Savio-Cardoz/theLink/components/epaper_driver_bsp/epaper_driver_bsp.h

#ifndef EPAPER_DRIVER_BSP_H
#define EPAPER_DRIVER_BSP_H

#include "driver/spi_master.h"
#include "driver/gpio.h"

/* Display color */
typedef enum {
    DRIVER_COLOR_WHITE  = 0xff,
    DRIVER_COLOR_BLACK  = 0x00,
    FONT_BACKGROUND = DRIVER_COLOR_WHITE,
}COLOR_IMAGE;

typedef struct {
    uint8_t cs;
    uint8_t dc;
    uint8_t rst;
    uint8_t busy;
    uint8_t mosi;
    uint8_t scl;
    int spi_host;
    int buffer_len;
}custom_lcd_spi_t;

class epaper_driver_display {
private:
    const custom_lcd_spi_t lcd_spi_data;
    const int Width;
    const int Height;
    spi_device_handle_t spi;
    uint8_t *buffer = NULL;

    void spi_gpio_init();
    void spi_port_init();
    void read_busy();

    esp_err_t spi_transmit_with_retry(spi_transaction_t *t, const char *what);

    void set_cs_1(){gpio_set_level((gpio_num_t)lcd_spi_data.cs,1);}
    void set_cs_0(){gpio_set_level((gpio_num_t)lcd_spi_data.cs,0);}
    void set_dc_1(){gpio_set_level((gpio_num_t)lcd_spi_data.dc,1);}
    void set_dc_0(){gpio_set_level((gpio_num_t)lcd_spi_data.dc,0);}
    void set_rst_1(){gpio_set_level((gpio_num_t)lcd_spi_data.rst,1);}
    void set_rst_0(){gpio_set_level((gpio_num_t)lcd_spi_data.rst,0);}

    void SPI_SendByte(uint8_t data);
    void EPD_SendData(uint8_t data);
    void EPD_SendCommand(uint8_t command);
    void writeBytes(uint8_t *buffer,int len);
    void writeBytes(const uint8_t *buffer, int len);
    void EPD_SetWindows(uint16_t Xstart, uint16_t Ystart, uint16_t Xend, uint16_t Yend);
    void EPD_SetCursor(uint16_t Xstart, uint16_t Ystart);
    void EPD_SetLut(const uint8_t *lut);
    void EPD_TurnOnDisplay();
    void EPD_TurnOnDisplayPart();

public:
    epaper_driver_display(int width, int height, custom_lcd_spi_t _lcd_spi_data);
    epaper_driver_display(int width, int height, custom_lcd_spi_t _lcd_spi_data, uint8_t *external_buffer);
    ~epaper_driver_display();

    void EPD_Init();    /* 墨水屏初始化 */
    void EPD_Clear();   /* 清空屏幕 */
    void EPD_Display(); /* 刷buffer到墨水屏 */
    
    /*局部刷新*/
    void EPD_DisplayPartBaseImage();
    void EPD_Init_Partial();
    void EPD_DisplayPart();
    void EPD_DrawColorPixel(uint16_t x, uint16_t y,uint8_t color);

    void EPD_LogHeap(const char *context);
};
#endif
