Savio-Cardoz/theLink/components/i2c_bsp/i2c_bsp.c

#include <string.h>

#include "driver/i2c_master.h"
#include "esp_log.h"
#include "freertos/FreeRTOS.h"
#include "freertos/task.h"

#include "i2c_bsp.h"

static const char *TAG = "I2C_BSP";

// Tag of the ESP-IDF I2C driver, silenced while sweeping so an absent device
// does not print an error per address.
static const char *DRIVER_TAG = "i2c.master";

// Mirrors the bus setup in the audio board support (components/codec_board/
// codec_init.c) so that a bus installed here behaves identically for the codec
// and RTC that share it.
#define I2C_BSP_GLITCH_IGNORE_CNT 7

// A probe of a present device finishes in a few hundred microseconds, so this
// only ever gets spent when a device holds the bus down.
#define I2C_BSP_SCAN_TIMEOUT_MS 20

// How many addresses must time out back to back before the sweep concludes the bus
// is stuck rather than busy. The driver reports "bus mutex unavailable" and "SDA
// held low" with the same error, and only the second is a wiring fault. A busy bus
// clears within one or two addresses, so a short run separates the two cases without
// needing to hold the bus quiet for longer than the sweep itself.
#define I2C_BSP_SCAN_STUCK_RUN 3

static i2c_master_bus_handle_t s_bus[I2C_BSP_MAX_PORTS];
static bool s_installed[I2C_BSP_MAX_PORTS];

esp_err_t i2c_bsp_init(uint8_t port, gpio_num_t sda, gpio_num_t scl)
{
    if (port >= I2C_BSP_MAX_PORTS)
    {
        ESP_LOGE(TAG, "I2C port %u out of range (max %d)", port, I2C_BSP_MAX_PORTS);
        return ESP_ERR_INVALID_ARG;
    }

    if (s_bus[port] != NULL)
    {
        return ESP_OK;
    }

    i2c_master_bus_config_t bus_config = {
        .clk_source = I2C_CLK_SRC_DEFAULT,
        .i2c_port = (i2c_port_num_t)port,
        .sda_io_num = sda,
        .scl_io_num = scl,
        .glitch_ignore_cnt = I2C_BSP_GLITCH_IGNORE_CNT,
        .flags.enable_internal_pullup = true,
    };

    i2c_master_bus_handle_t bus = NULL;
    esp_err_t err = i2c_new_master_bus(&bus_config, &bus);
    if (err == ESP_ERR_INVALID_STATE)
    {
        // Somebody got here first, most likely the audio board support, which
        // installs the bus itself from the audio task. Adopt their bus rather
        // than fighting over it.
        if (i2c_master_get_bus_handle((i2c_port_num_t)port, &bus) == ESP_OK && bus != NULL)
        {
            s_bus[port] = bus;
            s_installed[port] = false;
            ESP_LOGI(TAG, "Adopting existing I2C master bus on port %u", port);
            return ESP_OK;
        }
    }
    if (err != ESP_OK)
    {
        ESP_LOGE(TAG, "Failed to create I2C master bus on port %u: %s", port, esp_err_to_name(err));
        return err;
    }

    s_bus[port] = bus;
    s_installed[port] = true;
    ESP_LOGI(TAG, "I2C master bus %d up on SDA %d / SCL %d", port, sda, scl);
    return ESP_OK;
}

i2c_master_bus_handle_t i2c_bsp_bus(uint8_t port)
{
    if (port >= I2C_BSP_MAX_PORTS)
    {
        return NULL;
    }
    return s_bus[port];
}

void i2c_bsp_deinit(void)
{
    for (uint8_t port = 0; port < I2C_BSP_MAX_PORTS; port++)
    {
        if (!s_installed[port])
        {
            continue;
        }
        ESP_LOGI(TAG, "Deleting I2C master bus on port %u", port);
        i2c_del_master_bus(s_bus[port]);
        s_bus[port] = NULL;
        s_installed[port] = false;
    }
}

esp_err_t i2c_bsp_scan(uint8_t port, uint8_t first_addr, uint8_t last_addr,
                       uint8_t *found, size_t found_cap, size_t *found_count)
{
    if (port >= I2C_BSP_MAX_PORTS)
    {
        ESP_LOGE(TAG, "I2C port %u out of range (max %d)", port, I2C_BSP_MAX_PORTS);
        return ESP_ERR_INVALID_ARG;
    }
    if (first_addr > last_addr || last_addr > 0x7F)
    {
        ESP_LOGE(TAG, "I2C scan range 0x%02X..0x%02X is not a valid 7-bit range", first_addr, last_addr);
        return ESP_ERR_INVALID_ARG;
    }
    if (found == NULL || found_count == NULL)
    {
        return ESP_ERR_INVALID_ARG;
    }
    if (s_bus[port] == NULL)
    {
        return ESP_ERR_INVALID_STATE;
    }

    *found_count = 0;

    // The driver logs every address-only write that comes back NACKed, which on
    // a mostly empty bus is most of them. Mute it for the sweep only.
    const esp_log_level_t driver_level = esp_log_level_get(DRIVER_TAG);
    esp_log_level_set(DRIVER_TAG, ESP_LOG_NONE);

    esp_err_t ret = ESP_OK;
    size_t probed = 0;
    size_t nacked = 0;
    size_t timeouts = 0;
    unsigned consecutive_timeouts = 0;

    for (unsigned addr = first_addr; addr <= last_addr; addr++)
    {
        // The driver takes the bus mutex for the probe, so a codec write or a sensor
        // read still in flight makes the probe wait. Waits for that here rather
        // than reporting the resulting timeout as a missing device.
        (void)i2c_master_bus_wait_all_done(s_bus[port], pdMS_TO_TICKS(I2C_BSP_SCAN_TIMEOUT_MS));

        const esp_err_t err = i2c_master_probe(s_bus[port], (uint16_t)addr, I2C_BSP_SCAN_TIMEOUT_MS);
        probed++;
        if (err == ESP_OK)
        {
            consecutive_timeouts = 0;
            ESP_LOGD(TAG, "0x%02X acknowledged", addr);
            if (*found_count < found_cap)
            {
                found[(*found_count)++] = (uint8_t)addr;
            }
            else
            {
                // Not fatal, but the list is now incomplete, so a reader must not
                // treat it as proof the bus holds nothing else.
                ESP_LOGW(TAG, "more than %zu devices answered, the list is truncated", found_cap);
                ret = ESP_ERR_INVALID_SIZE;
            }
            continue;
        }

        if (err == ESP_ERR_TIMEOUT)
        {
            // The driver reports a bus mutex timeout as ESP_ERR_TIMEOUT too, so this
            // is not on its own evidence of a broken bus. Only a run of them is: a
            // genuine stuck-bus fault keeps timing out at every address, whereas a
            // busy bus recovers.
            timeouts++;
            consecutive_timeouts++;
            ESP_LOGD(TAG, "0x%02X timed out (bus busy, or held low)", addr);
            if (consecutive_timeouts >= I2C_BSP_SCAN_STUCK_RUN)
            {
                ret = ESP_ERR_TIMEOUT;
                break;
            }
            continue;
        }

        consecutive_timeouts = 0;
        nacked++;
        ESP_LOGD(TAG, "0x%02X did not acknowledge", addr);
    }

    // Every result, not just the hits. A sweep that reports five addresses is
    // indistinguishable from one that silently stopped early unless the misses are
    // visible too, which is what makes an absent device tellable apart from a probe
    // that never ran.
    ESP_LOGI(TAG, "swept 0x%02X..0x%02X: %zu answered, %zu did not acknowledge, %zu timed out",
             first_addr, last_addr, probed - nacked - timeouts, nacked, timeouts);

    esp_log_level_set(DRIVER_TAG, driver_level);
    return ret;
}
