Savio-Cardoz/theLink/main/provisioning.cpp

#include <stdio.h>
#include <string.h>
#include <atomic>

#include "freertos/FreeRTOS.h"
#include "freertos/task.h"
#include "freertos/event_groups.h"

#include "esp_log.h"
#include "esp_err.h"
#include "esp_wifi.h"
#include "esp_event.h"
#include "esp_system.h"
#include "esp_heap_caps.h"

#include <network_provisioning/manager.h>
#include <network_provisioning/scheme_ble.h>
#include "qrcode.h"

#include "lvgl.h"

#include "app_common.hpp"
#include "download_mgr.hpp"
#include "mqtt_io.hpp"
#include "ui_port.hpp"

#include "provisioning.hpp"

static const char *TAG = "app";

static std::atomic<led_prov_state_t> s_led_prov_state{led_prov_state_t::LED_PROV_STATE_NONE};

static void (*s_post_provision_hook)(void) = nullptr;

uint32_t prov_pulse_period_ms(led_prov_state_t state)
{
	switch (state) {
	case led_prov_state_t::LED_PROV_STATE_PROVISIONING:   return 500;
	case led_prov_state_t::LED_PROV_STATE_BLE_CONNECTED:  return 1500;
	case led_prov_state_t::LED_PROV_STATE_WIFI_CONNECTED: return 3000;
	default:                                              return 0;
	}
}

void prov_set_led_state(led_prov_state_t state)
{
	s_led_prov_state.store(state);
}

led_prov_state_t prov_get_led_state(void)
{
	return s_led_prov_state.load();
}

// ── Wi-Fi provisioning definitions ──────────────────────────────────
#if CONFIG_EXAMPLE_PROV_SECURITY_VERSION_2
#if CONFIG_EXAMPLE_PROV_SEC2_DEV_MODE
#define PROV_SEC2_USERNAME "wifiprov"
#define PROV_SEC2_PWD "abcd1234"

/* This salt,verifier has been generated for username = "wifiprov" and password = "abcd1234"
 * IMPORTANT NOTE: For production cases, this must be unique to every device
 * and should come from device manufacturing partition.*/
static const char sec2_salt[] = {
	0x03, 0x6e, 0xe0, 0xc7, 0xbc, 0xb9, 0xed, 0xa8, 0x4c, 0x9e, 0xac, 0x97, 0xd9, 0x3d, 0xec, 0xf4};

static const char sec2_verifier[] = {
	0x7c, 0x7c, 0x85, 0x47, 0x65, 0x08, 0x94, 0x6d, 0xd6, 0x36, 0xaf, 0x37, 0xd7, 0xe8, 0x91, 0x43,
	0x78, 0xcf, 0xfd, 0x61, 0x6c, 0x59, 0xd2, 0xf8, 0x39, 0x08, 0x12, 0x72, 0x38, 0xde, 0x9e, 0x24,
	0xa4, 0x70, 0x26, 0x1c, 0xdf, 0xa9, 0x03, 0xc2, 0xb2, 0x70, 0xe7, 0xb1, 0x32, 0x24, 0xda, 0x11,
	0x1d, 0x97, 0x18, 0xdc, 0x60, 0x72, 0x08, 0xcc, 0x9a, 0xc9, 0x0c, 0x48, 0x27, 0xe2, 0xae, 0x89,
	0xaa, 0x16, 0x25, 0xb8, 0x04, 0xd2, 0x1a, 0x9b, 0x3a, 0x8f, 0x37, 0xf6, 0xe4, 0x3a, 0x71, 0x2e,
	0xe1, 0x27, 0x86, 0x6e, 0xad, 0xce, 0x28, 0xff, 0x54, 0x46, 0x60, 0x1f, 0xb9, 0x96, 0x87, 0xdc,
	0x57, 0x40, 0xa7, 0xd4, 0x6c, 0xc9, 0x77, 0x54, 0xdc, 0x16, 0x82, 0xf0, 0xed, 0x35, 0x6a, 0xc4,
	0x70, 0xad, 0x3d, 0x90, 0xb5, 0x81, 0x94, 0x70, 0xd7, 0xbc, 0x65, 0xb2, 0xd5, 0x18, 0xe0, 0x2e,
	0xc3, 0xa5, 0xf9, 0x68, 0xdd, 0x64, 0x7b, 0xb8, 0xb7, 0x3c, 0x9c, 0xfc, 0x00, 0xd8, 0x71, 0x7e,
	0xb7, 0x9a, 0x7c, 0xb1, 0xb7, 0xc2, 0xc3, 0x18, 0x34, 0x29, 0x32, 0x43, 0x3e, 0x00, 0x99, 0xe9,
	0x82, 0x94, 0xe3, 0xd8, 0x2a, 0xb0, 0x96, 0x29, 0xb7, 0xdf, 0x0e, 0x5f, 0x08, 0x33, 0x40, 0x76,
	0x52, 0x91, 0x32, 0x00, 0x9f, 0x97, 0x2c, 0x89, 0x6c, 0x39, 0x1e, 0xc8, 0x28, 0x05, 0x44, 0x17,
	0x3f, 0x68, 0x02, 0x8a, 0x9f, 0x44, 0x61, 0xd1, 0xf5, 0xa1, 0x7e, 0x5a, 0x70, 0xd2, 0xc7, 0x23,
	0x81, 0xcb, 0x38, 0x68, 0xe4, 0x2c, 0x20, 0xbc, 0x40, 0x57, 0x76, 0x17, 0xbd, 0x08, 0xb8, 0x96,
	0xbc, 0x26, 0xeb, 0x32, 0x46, 0x69, 0x35, 0x05, 0x8c, 0x15, 0x70, 0xd9, 0x1b, 0xe9, 0xbe, 0xcc,
	0xa9, 0x38, 0xa6, 0x67, 0xf0, 0xad, 0x50, 0x13, 0x19, 0x72, 0x64, 0xbf, 0x52, 0xc2, 0x34, 0xe2,
	0x1b, 0x11, 0x79, 0x74, 0x72, 0xbd, 0x34, 0x5b, 0xb1, 0xe2, 0xfd, 0x66, 0x73, 0xfe, 0x71, 0x64,
	0x74, 0xd0, 0x4e, 0xbc, 0x51, 0x24, 0x19, 0x40, 0x87, 0x0e, 0x92, 0x40, 0xe6, 0x21, 0xe7, 0x2d,
	0x4e, 0x37, 0x76, 0x2f, 0x2e, 0xe2, 0x68, 0xc7, 0x89, 0xe8, 0x32, 0x13, 0x42, 0x06, 0x84, 0x84,
	0x53, 0x4a, 0xb3, 0x0c, 0x1b, 0x4c, 0x8d, 0x1c, 0x51, 0x97, 0x19, 0xab, 0xae, 0x77, 0xff, 0xdb,
	0xec, 0xf0, 0x10, 0x95, 0x34, 0x33, 0x6b, 0xcb, 0x3e, 0x84, 0x0f, 0xb9, 0xd8, 0x5f, 0xb8, 0xa0,
	0xb8, 0x55, 0x53, 0x3e, 0x70, 0xf7, 0x18, 0xf5, 0xce, 0x7b, 0x4e, 0xbf, 0x27, 0xce, 0xce, 0xa8,
	0xb3, 0xbe, 0x40, 0xc5, 0xc5, 0x32, 0x29, 0x3e, 0x71, 0x64, 0x9e, 0xde, 0x8c, 0xf6, 0x75, 0xa1,
	0xe6, 0xf6, 0x53, 0xc8, 0x31, 0xa8, 0x78, 0xde, 0x50, 0x40, 0xf7, 0x62, 0xde, 0x36, 0xb2, 0xba};
#endif

static esp_err_t example_get_sec2_salt(const char **salt, uint16_t *salt_len)
{
#if CONFIG_EXAMPLE_PROV_SEC2_DEV_MODE
	ESP_LOGI(TAG, "Development mode: using hard coded salt");
	*salt = sec2_salt;
	*salt_len = sizeof(sec2_salt);
	return ESP_OK;
#elif CONFIG_EXAMPLE_PROV_SEC2_PROD_MODE
	ESP_LOGE(TAG, "Not implemented!");
	return ESP_FAIL;
#endif
}

static esp_err_t example_get_sec2_verifier(const char **verifier, uint16_t *verifier_len)
{
#if CONFIG_EXAMPLE_PROV_SEC2_DEV_MODE
	ESP_LOGI(TAG, "Development mode: using hard coded verifier");
	*verifier = sec2_verifier;
	*verifier_len = sizeof(sec2_verifier);
	return ESP_OK;
#elif CONFIG_EXAMPLE_PROV_SEC2_PROD_MODE
	/* This code needs to be updated with appropriate implementation to provide verifier */
	ESP_LOGE(TAG, "Not implemented!");
	return ESP_FAIL;
#endif
}
#endif

// Persistent structures for the live binary QR matrix layout engine
static lv_image_dsc_t qr_dynamic_bmp;
static uint8_t *qr_pixel_buffer = NULL;
static lv_obj_t *qr_image_obj = NULL;

#define PROV_QR_VERSION "v1"
#define PROV_TRANSPORT_SOFTAP "softap"
#define PROV_TRANSPORT_BLE "ble"
#define QRCODE_BASE_URL "https://espressif.github.io/esp-jumpstart/qrcode.html"

/* How long to keep retrying the MQTT client start. 1 s apart, so this covers
 * both ways provisioning ends: the client hanging up (a few seconds) and the
 * network_provisioning auto-stop timer (CONFIG_NETWORK_PROV_AUTOSTOP_TIMEOUT,
 * 30 s by default). */
#define MQTT_START_MAX_ATTEMPTS 60

/* Signal Wi-Fi events on this event-group */
const int WIFI_CONNECTED_EVENT = BIT0;
static EventGroupHandle_t wifi_event_group;

static void wifi_init_sta(void)
{
	/* Start Wi-Fi in station mode */
	ESP_ERROR_CHECK(esp_wifi_set_mode(WIFI_MODE_STA));
	ESP_ERROR_CHECK(esp_wifi_start());
}

static void wifi_prov_task(void *arg);

static void get_device_service_name(char *service_name, size_t max)
{
	uint8_t eth_mac[6];
	const char *ssid_prefix = "PROV_";
	esp_wifi_get_mac(WIFI_IF_STA, eth_mac);
	snprintf(service_name, max, "%s%02X%02X%02X",
			 ssid_prefix, eth_mac[3], eth_mac[4], eth_mac[5]);
}

/* Handler for the optional provisioning endpoint registered by the application.
 * The data format can be chosen by applications. Here, we are using plain ascii text.
 * Applications can choose to use other formats like protobuf, JSON, XML, etc.
 * Note that memory for the response buffer must be allocated using heap as this buffer
 * gets freed by the protocomm layer once it has been sent by the transport layer.
 */
esp_err_t custom_prov_data_handler(uint32_t session_id, const uint8_t *inbuf, ssize_t inlen,
								   uint8_t **outbuf, ssize_t *outlen, void *priv_data)
{
	if (inbuf)
	{
		ESP_LOGI(TAG, "Received data: %.*s", inlen, (char *)inbuf);
	}
	char response[] = "SUCCESS";
	*outbuf = (uint8_t *)strdup(response);
	if (*outbuf == NULL)
	{
		ESP_LOGE(TAG, "System out of memory");
		return ESP_ERR_NO_MEM;
	}
	*outlen = strlen(response) + 1; /* +1 for NULL terminating byte */

	return ESP_OK;
}

static void qr_code_lvgl_display_cb(esp_qrcode_handle_t qrcode) {
    int qr_size = esp_qrcode_get_size(qrcode);
    const int display_dim = 200;

    ESP_LOGI("QR_UI", "callback entered: qr_size=%d, SPIRAM free=%u",
             qr_size, (unsigned)heap_caps_get_free_size(MALLOC_CAP_SPIRAM));

    int scale = display_dim / qr_size;
    if (scale < 1) scale = 1;

    int offset_x = (display_dim - (qr_size * scale)) / 2;
    int offset_y = (display_dim - (qr_size * scale)) / 2;

    const size_t RGB565_SIZE = display_dim * display_dim * 2;

    if (qr_pixel_buffer == NULL) {
        qr_pixel_buffer = (uint8_t *)heap_caps_malloc(RGB565_SIZE, MALLOC_CAP_SPIRAM);
    }

    if (qr_pixel_buffer == NULL) {
        ESP_LOGE("QR_UI", "External frame allocation breakdown for QR matrix layer!");
        return;
    }

    ESP_LOGI("QR_UI", "qr_pixel_buffer=%p, scale=%d, offset=(%d,%d)",
             (void *)qr_pixel_buffer, scale, offset_x, offset_y);

    uint16_t *rgb565_dest = (uint16_t *)qr_pixel_buffer;
    for (int i = 0; i < (display_dim * display_dim); i++) {
        rgb565_dest[i] = 0xFFFF; // Clear canvas background to complete white
    }

    for (int y = 0; y < qr_size; y++) {
        for (int x = 0; x < qr_size; x++) {
            if (esp_qrcode_get_module(qrcode, x, y)) {
                for (int py = 0; py < scale; py++) {
                    for (int px = 0; px < scale; px++) {
                        int target_x = offset_x + (x * scale) + px;
                        int target_y = offset_y + (y * scale) + py;
                        if (target_x >= 0 && target_x < display_dim && target_y >= 0 && target_y < display_dim) {
                            rgb565_dest[target_y * display_dim + target_x] = 0x0000; // Map black module bits
                        }
                    }
                }
            }
        }
    }

    qr_dynamic_bmp.header.magic = LV_IMAGE_HEADER_MAGIC;
    qr_dynamic_bmp.header.cf = LV_COLOR_FORMAT_RGB565;
    qr_dynamic_bmp.header.flags = 0;
    qr_dynamic_bmp.header.w = display_dim;
    qr_dynamic_bmp.header.h = display_dim;
    qr_dynamic_bmp.header.stride = display_dim * 2;
    qr_dynamic_bmp.header.reserved_2 = 0;
    qr_dynamic_bmp.data_size = RGB565_SIZE;
    qr_dynamic_bmp.data = qr_pixel_buffer;

    bool locked = ui_lock(-1);
    ESP_LOGI("QR_UI", "ui_lock returned %d", locked);

    if (locked) {
        if (qr_image_obj == NULL) {
            qr_image_obj = lv_image_create(lv_screen_active());
        }

        lv_image_set_src(qr_image_obj, NULL);
        lv_image_set_src(qr_image_obj, &qr_dynamic_bmp);
        lv_obj_center(qr_image_obj);
        lv_obj_move_foreground(qr_image_obj);
        lv_obj_clear_flag(qr_image_obj, LV_OBJ_FLAG_HIDDEN);
        lv_obj_invalidate(qr_image_obj);

        ui_unlock();
        ESP_LOGI("QR_UI", "Successfully pushed binary QR image payload onto layout engine matrix.");
    }
}

static void wifi_prov_print_qr(const char *name, const char *username, const char *pop, const char *transport)
{
	if (!name || !transport)
	{
		ESP_LOGW(TAG, "Cannot generate QR code payload. Data missing.");
		return;
	}
	char payload[150] = {0};
	if (pop)
	{
#if CONFIG_EXAMPLE_PROV_SECURITY_VERSION_1
		snprintf(payload, sizeof(payload), "{\"ver\":\"%s\",\"name\":\"%s\""
										   ",\"pop\":\"%s\",\"transport\":\"%s\"}",
				 PROV_QR_VERSION, name, pop, transport);
#elif CONFIG_EXAMPLE_PROV_SECURITY_VERSION_2
		snprintf(payload, sizeof(payload), "{\"ver\":\"%s\",\"name\":\"%s\""
										   ",\"username\":\"%s\",\"pop\":\"%s\",\"transport\":\"%s\"}",
				 PROV_QR_VERSION, name, username, pop, transport);
#endif
	}
	else
	{
		snprintf(payload, sizeof(payload), "{\"ver\":\"%s\",\"name\":\"%s\""
										   ",\"transport\":\"%s\",\"network\":\"wifi\"}",
				 PROV_QR_VERSION, name, transport);
	}

	ESP_LOGI(TAG, "Scan this QR code from the provisioning application for Provisioning.");
	esp_qrcode_config_t cfg = ESP_QRCODE_CONFIG_DEFAULT();
	cfg.display_func = qr_code_lvgl_display_cb;
	esp_qrcode_generate(&cfg, payload);
	ESP_LOGI(TAG, "If QR code is not visible, copy paste the below URL in a browser.\n%s?data=%s", QRCODE_BASE_URL, payload);
}

#ifdef CONFIG_EXAMPLE_PROV_ENABLE_APP_CALLBACK
void wifi_prov_app_callback(void *user_data, wifi_prov_cb_event_t event, void *event_data)
{
	/**
	 * This is blocking callback, any configurations that needs to be set when a particular
	 * provisioning event is triggered can be set here.
	 */
	switch (event)
	{
	case WIFI_PROV_SET_STA_CONFIG:
	{
		/**
		 * Wi-Fi configurations can be set here before the Wi-Fi is enabled in
		 * STA mode.
		 */
		wifi_config_t *wifi_config = (wifi_config_t *)event_data;
		(void)wifi_config;
		break;
	}
	default:
		break;
	}
}

const wifi_prov_event_handler_t wifi_prov_event_handler = {
	.event_cb = wifi_prov_app_callback,
	.user_data = NULL,
};
#endif /* EXAMPLE_PROV_ENABLE_APP_CALLBACK */

static void event_handler(void *arg, esp_event_base_t event_base,
						  int32_t event_id, void *event_data)
{
	if (event_base == NETWORK_PROV_EVENT)
	{
		switch (event_id)
		{
		case NETWORK_PROV_START:
			ESP_LOGI(TAG, "Provisioning started");
			prov_set_led_state(led_prov_state_t::LED_PROV_STATE_PROVISIONING);
			break;
		case NETWORK_PROV_WIFI_CRED_RECV:
		{
			wifi_sta_config_t *wifi_sta_cfg = (wifi_sta_config_t *)event_data;
			ESP_LOGI(TAG, "Received Wi-Fi credentials"
						  "\n\tSSID     : %s\n\tPassword : %s",
					 (const char *)wifi_sta_cfg->ssid,
					 (const char *)wifi_sta_cfg->password);
			break;
		}
		case NETWORK_PROV_WIFI_CRED_FAIL:
		{
			network_prov_wifi_sta_fail_reason_t *reason = (network_prov_wifi_sta_fail_reason_t *)event_data;
			ESP_LOGE(TAG, "Provisioning failed!\n\tReason : %s"
						  "\n\tPlease reset to factory and retry provisioning",
					 (*reason == NETWORK_PROV_WIFI_STA_AUTH_ERROR) ? "Wi-Fi station authentication failed" : "Wi-Fi access-point not found");
#ifdef CONFIG_EXAMPLE_RESET_PROV_MGR_ON_FAILURE
			/* Reset the state machine on provisioning failure.
			 * This is enabled by the CONFIG_EXAMPLE_RESET_PROV_MGR_ON_FAILURE configuration.
			 * It allows the provisioning manager to retry the provisioning process
			 * based on the number of attempts specified in wifi_conn_attempts. After attempting
			 * the maximum number of retries, the provisioning manager will reset the state machine
			 * and the provisioning process will be terminated.
			 */
			network_prov_mgr_reset_wifi_sm_state_on_failure();
#endif
			break;
		}
		case NETWORK_PROV_WIFI_CRED_SUCCESS:
			ESP_LOGI(TAG, "Provisioning successful");
			break;
		case NETWORK_PROV_END:
		{
			/* De-initialize manager once provisioning is finished */
			esp_err_t err = network_prov_mgr_deinit();
			if (err != ESP_OK)
			{
				ESP_LOGE(TAG, "Failed to de-initialize provisioning manager: %s", esp_err_to_name(err));
			}

			// Clean up the binary image widget & its PSRAM allocation buffer
            if (ui_lock(-1))
            {
                if (qr_image_obj != NULL)
                {
                    lv_obj_delete(qr_image_obj);
                    qr_image_obj = NULL;
                }
                if (qr_pixel_buffer != NULL)
                {
                    heap_caps_free(qr_pixel_buffer);
                    qr_pixel_buffer = NULL;
                }
                lv_obj_invalidate(lv_screen_active());
                ui_unlock();
            }
			break;
		}
		default:
			break;
		}
	}
	else if (event_base == WIFI_EVENT)
	{
		switch (event_id)
		{
		case WIFI_EVENT_STA_START:
			esp_wifi_connect();
			break;
		case WIFI_EVENT_STA_DISCONNECTED:
			{
				ESP_LOGI(TAG, "Disconnected. Connecting to the AP again...");
				ui_notify_network_status(false);
				esp_wifi_connect();
			}
			break;
#ifdef CONFIG_EXAMPLE_PROV_TRANSPORT_SOFTAP
		case WIFI_EVENT_AP_STACONNECTED:
			ESP_LOGI(TAG, "SoftAP transport: Connected!");
			break;
		case WIFI_EVENT_AP_STADISCONNECTED:
			ESP_LOGI(TAG, "SoftAP transport: Disconnected!");
			break;
#endif
		default:
			break;
		}
	}
	else if (event_base == IP_EVENT && event_id == IP_EVENT_STA_GOT_IP)
	{
		ip_event_got_ip_t *event = (ip_event_got_ip_t *)event_data;
		ESP_LOGI(TAG, "Connected with IP Address:" IPSTR, IP2STR(&event->ip_info.ip));

		ui_notify_network_status(true);

		/* Signal main application to continue execution */
		xEventGroupSetBits(wifi_event_group, WIFI_CONNECTED_EVENT);
		prov_set_led_state(led_prov_state_t::LED_PROV_STATE_WIFI_CONNECTED);
#ifdef CONFIG_EXAMPLE_PROV_TRANSPORT_BLE
	}
	else if (event_base == PROTOCOMM_TRANSPORT_BLE_EVENT)
	{
		switch (event_id)
		{
		case PROTOCOMM_TRANSPORT_BLE_CONNECTED:
			ESP_LOGI(TAG, "BLE transport: Connected!");
			/*
			 * Pre-keygen snapshot. The repeated "BLE_INIT: Malloc failed"
			 * fires ~330 ms after this, while security2 derives the SRP
			 * public key, so the BTCAP/DMA figures here are the best
			 * available predictor of whether that allocation will succeed.
			 */
			download::log_heap_info("BLE transport connected (pre-keygen)");
			prov_set_led_state(led_prov_state_t::LED_PROV_STATE_BLE_CONNECTED);
			break;
		case PROTOCOMM_TRANSPORT_BLE_DISCONNECTED:
			ESP_LOGI(TAG, "BLE transport: Disconnected!");
			/*
			 * Post-mortem: if BTCAP free is not back where it was at
			 * connect time, a failed handshake leaked controller memory and
			 * the next attempt is guaranteed to fail earlier than this one.
			 */
			download::log_heap_info("BLE transport disconnected (post-mortem)");
			break;
		default:
			break;
		}
#endif
	}
	else if (event_base == PROTOCOMM_SECURITY_SESSION_EVENT)
	{
		switch (event_id)
		{
		case PROTOCOMM_SECURITY_SESSION_SETUP_OK:
			ESP_LOGI(TAG, "Secured session established!");
			/*
			 * The last point before prov-scan. That endpoint triggers a
			 * Wi-Fi active scan and then security2 must AES-GCM encrypt the
			 * resulting SSID list. Both failure modes (esp-aes and
			 * BLE_INIT) appear immediately after this line, while the scan
			 * is allocating, so snapshot the pools right here.
			 */
			download::log_heap_info("security session established (pre prov-scan)");
			break;
		case PROTOCOMM_SECURITY_SESSION_INVALID_SECURITY_PARAMS:
			ESP_LOGE(TAG, "Received invalid security parameters for establishing secure session!");
			break;
		case PROTOCOMM_SECURITY_SESSION_CREDENTIALS_MISMATCH:
			ESP_LOGE(TAG, "Received incorrect username and/or PoP for establishing secure session!");
			break;
		default:
			break;
		}
	}
}

void provisioning_register_core_events(void)
{
	wifi_event_group = xEventGroupCreate();

	/* Register our event handler for Wi-Fi, IP and Provisioning related events */
	ESP_ERROR_CHECK(esp_event_handler_register(NETWORK_PROV_EVENT, ESP_EVENT_ANY_ID, &event_handler, NULL));
#ifdef CONFIG_EXAMPLE_PROV_TRANSPORT_BLE
	ESP_ERROR_CHECK(esp_event_handler_register(PROTOCOMM_TRANSPORT_BLE_EVENT, ESP_EVENT_ANY_ID, &event_handler, NULL));
#endif
	ESP_ERROR_CHECK(esp_event_handler_register(PROTOCOMM_SECURITY_SESSION_EVENT, ESP_EVENT_ANY_ID, &event_handler, NULL));
	ESP_ERROR_CHECK(esp_event_handler_register(IP_EVENT, IP_EVENT_STA_GOT_IP, &event_handler, NULL));

	// Hand the notification LED back to MQTT control once the app is up.
	app::register_on_connect([]()
		{
			prov_set_led_state(led_prov_state_t::LED_PROV_STATE_NONE);
		});
}

void provisioning_start(void)
{
	xTaskCreate(wifi_prov_task, "wifi_prov", 4096, NULL, 5, NULL);
}

void provisioning_set_post_provision_hook(void (*hook)(void))
{
	s_post_provision_hook = hook;
}

static void wifi_prov_task(void *arg)
{
	/* Configuration for the provisioning manager */
	network_prov_mgr_config_t config = {
	/* What is the Provisioning Scheme that we want ?
	 * network_prov_scheme_softap or network_prov_scheme_ble */
#ifdef CONFIG_EXAMPLE_PROV_TRANSPORT_BLE
		.scheme = network_prov_scheme_ble,
#endif /* CONFIG_EXAMPLE_PROV_TRANSPORT_BLE */
#ifdef CONFIG_EXAMPLE_PROV_TRANSPORT_SOFTAP
		.scheme = network_prov_scheme_softap,
#endif /* CONFIG_EXAMPLE_PROV_TRANSPORT_SOFTAP */
#ifdef CONFIG_EXAMPLE_PROV_ENABLE_APP_CALLBACK
		.app_event_handler = wifi_prov_event_handler,
#endif /* EXAMPLE_PROV_ENABLE_APP_CALLBACK */

	/* Any default scheme specific event handler that you would
	 * like to choose. Since our example application requires
	 * neither BT nor BLE, we can choose to release the associated
	 * memory once provisioning is complete, or not needed
	 * (in case when device is already provisioned). Choosing
	 * appropriate scheme specific event handler allows the manager
	 * to take care of this automatically. This can be set to
	 * NETWORK_PROV_EVENT_HANDLER_NONE when using network_prov_scheme_softap*/
#ifdef CONFIG_EXAMPLE_PROV_TRANSPORT_BLE
		.scheme_event_handler = NETWORK_PROV_SCHEME_BLE_EVENT_HANDLER_FREE_BTDM,
#endif /* CONFIG_EXAMPLE_PROV_TRANSPORT_BLE */
#ifdef CONFIG_EXAMPLE_PROV_TRANSPORT_SOFTAP
		.scheme_event_handler = NETWORK_PROV_EVENT_HANDLER_NONE,
#endif /* CONFIG_EXAMPLE_PROV_TRANSPORT_SOFTAP */
#ifdef CONFIG_EXAMPLE_RESET_PROV_MGR_ON_FAILURE
		.network_prov_wifi_conn_cfg = {
			.wifi_conn_attempts = CONFIG_EXAMPLE_PROV_MGR_CONNECTION_CNT}
#endif
	};

	/*
	 * Bracket the provisioning manager bring-up. network_prov_mgr_init()
	 * claims the Wi-Fi netif and configures the BLE scheme, and
	 * network_prov_mgr_start_provisioning() below is what actually starts
	 * the BT controller. The latter is where the ~5.8 KB INTERNAL drop on a
	 * provisioning boot comes from; BTDM itself stays resident until the
	 * provisioning timer expires, so what is logged here is what the AES DMA
	 * descriptors and the controller will have to share later.
	 */
	download::log_heap_info("before network_prov_mgr_init");

	/* Initialize provisioning manager with the
	 * configuration parameters set above */
	ESP_ERROR_CHECK(network_prov_mgr_init(config));

	download::log_heap_info("after network_prov_mgr_init");

	bool provisioned = false;
#ifdef CONFIG_EXAMPLE_RESET_PROVISIONED
	network_prov_mgr_reset_wifi_provisioning();
#else
	/* Let's find out if the device is provisioned */
	ESP_ERROR_CHECK(network_prov_mgr_is_wifi_provisioned(&provisioned));

#endif
	/* If device is not yet provisioned start provisioning service */
	if (!provisioned)
	{
		ESP_LOGI(TAG, "Starting provisioning");

		/* What is the Device Service Name that we want
		 * This translates to :
		 *     - Wi-Fi SSID when scheme is network_prov_scheme_softap
		 *     - device name when scheme is network_prov_scheme_ble
		 */
		char service_name[12];
		get_device_service_name(service_name, sizeof(service_name));

#ifdef CONFIG_EXAMPLE_PROV_SECURITY_VERSION_1
		/* What is the security level that we want (0, 1, 2):
		 *      - NETWORK_PROV_SECURITY_0 is simply plain text communication.
		 *      - NETWORK_PROV_SECURITY_1 is secure communication which consists of secure handshake
		 *          using X25519 key exchange and proof of possession (pop) and AES-CTR
		 *          for encryption/decryption of messages.
		 *      - NETWORK_PROV_SECURITY_2 SRP6a based authentication and key exchange
		 *        + AES-GCM encryption/decryption of messages
		 */
		network_prov_security_t security = NETWORK_PROV_SECURITY_1;

		/* Do we want a proof-of-possession (ignored if Security 0 is selected):
		 *      - this should be a string with length > 0
		 *      - NULL if not used
		 */
		const char *pop = "abcd1234";

		/* This is the structure for passing security parameters
		 * for the protocomm security 1.
		 */
		network_prov_security1_params_t *sec_params = pop;

		const char *username = NULL;

#elif CONFIG_EXAMPLE_PROV_SECURITY_VERSION_2
		network_prov_security_t security = NETWORK_PROV_SECURITY_2;
		/* The username must be the same one, which has been used in the generation of salt and verifier */

#if CONFIG_EXAMPLE_PROV_SEC2_DEV_MODE
		/* This pop field represents the password that will be used to generate salt and verifier.
		 * The field is present here in order to generate the QR code containing password.
		 * In production this password field shall not be stored on the device */
		const char *username = PROV_SEC2_USERNAME;
		const char *pop = PROV_SEC2_PWD;
#elif CONFIG_EXAMPLE_PROV_SEC2_PROD_MODE
		/* The username and password shall not be embedded in the firmware,
		 * they should be provided to the user by other means.
		 * e.g. QR code sticker */
		const char *username = NULL;
		const char *pop = NULL;
#endif
		/* This is the structure for passing security parameters
		 * for the protocomm security 2.
		 * If dynamically allocated, sec2_params pointer and its content
		 * must be valid till NETWORK_PROV_END event is triggered.
		 */
		network_prov_security2_params_t sec2_params = {};

		ESP_ERROR_CHECK(example_get_sec2_salt(&sec2_params.salt, &sec2_params.salt_len));
		ESP_ERROR_CHECK(example_get_sec2_verifier(&sec2_params.verifier, &sec2_params.verifier_len));

		network_prov_security2_params_t *sec_params = &sec2_params;
#endif
		/* What is the service key (could be NULL)
		 * This translates to :
		 *     - Wi-Fi password when scheme is network_prov_scheme_softap
		 *          (Minimum expected length: 8, maximum 64 for WPA2-PSK)
		 *     - simply ignored when scheme is network_prov_scheme_ble
		 */
		const char *service_key = NULL;

#ifdef CONFIG_EXAMPLE_PROV_TRANSPORT_BLE
		/* This step is only useful when scheme is network_prov_scheme_ble. This will
		 * set a custom 128 bit UUID which will be included in the BLE advertisement
		 * and will correspond to the primary GATT service that provides provisioning
		 * endpoints as GATT characteristics. Each GATT characteristic will be
		 * formed using the primary service UUID as base, with different auto assigned
		 * 12th and 13th bytes (assume counting starts from 0th byte). The client side
		 * applications must identify the endpoints by reading the User Characteristic
		 * Description descriptor (0x2901) for each characteristic, which contains the
		 * endpoint name of the characteristic */
		uint8_t custom_service_uuid[] = {
			/* LSB <---------------------------------------
			 * ---------------------------------------> MSB */
			0xb4,
			0xdf,
			0x5a,
			0x1c,
			0x3f,
			0x6b,
			0xf4,
			0xbf,
			0xea,
			0x4a,
			0x82,
			0x03,
			0x04,
			0x90,
			0x1a,
			0x02,
		};

		/* If your build fails with linker errors at this point, then you may have
		 * forgotten to enable the BT stack or BTDM BLE settings in the SDK (e.g. see
		 * the sdkconfig.defaults in the example project) */
		network_prov_scheme_ble_set_service_uuid(custom_service_uuid);
#endif /* CONFIG_EXAMPLE_PROV_TRANSPORT_BLE */

		/* An optional endpoint that applications can create if they expect to
		 * get some additional custom data during provisioning workflow.
		 * The endpoint name can be anything of your choice.
		 * This call must be made before starting the provisioning.
		 */
		network_prov_mgr_endpoint_create("custom-data");

		/* Start provisioning service */
		ESP_ERROR_CHECK(network_prov_mgr_start_provisioning(security, (const void *)sec_params, service_name, service_key));

		/* BT controller is now resident: this is the baseline that every
		 * later esp-aes / BLE_INIT allocation must fit into. */
		download::log_heap_info("after network_prov_mgr_start_provisioning");

		/* The handler for the optional endpoint created above.
		 * This call must be made after starting the provisioning, and only if the endpoint
		 * has already been created above.
		 */
		network_prov_mgr_endpoint_register("custom-data", custom_prov_data_handler, NULL);

		/* Uncomment the following to wait for the provisioning to finish and then release
		 * the resources of the manager. Since in this case de-initialization is triggered
		 * by the default event loop handler, we don't need to call the following */
		// network_prov_mgr_wait();
		// network_prov_mgr_deinit();
		/* Print QR code for provisioning */
#ifdef CONFIG_EXAMPLE_PROV_TRANSPORT_BLE
		wifi_prov_print_qr(service_name, username, pop, PROV_TRANSPORT_BLE);
#else  /* CONFIG_EXAMPLE_PROV_TRANSPORT_SOFTAP */
		wifi_prov_print_qr(service_name, username, pop, PROV_TRANSPORT_SOFTAP);
#endif /* CONFIG_EXAMPLE_PROV_TRANSPORT_BLE */
	}
	else
	{
		ESP_LOGI(TAG, "Already provisioned, starting Wi-Fi STA");

		/* We don't need the manager as device is already provisioned,
		 * so let's release it's resources */
		ESP_ERROR_CHECK(network_prov_mgr_deinit());

		ESP_ERROR_CHECK(esp_event_handler_register(WIFI_EVENT, ESP_EVENT_ANY_ID, &event_handler, NULL));
		/* Start Wi-Fi station */
		wifi_init_sta();
	}

	/* Wait for Wi-Fi connection */
	xEventGroupWaitBits(wifi_event_group, WIFI_CONNECTED_EVENT, true, true, portMAX_DELAY);

	if (!provisioned)
	{
		/*
		 * We have just come through BLE provisioning. The
		 * NETWORK_PROV_SCHEME_BLE_EVENT_HANDLER_FREE_BTDM handler has released the
		 * controller, but the internal pool it leaves behind is badly fragmented and
		 * the app's subsystems no longer fit alongside what is left. Measured on the
		 * ESP32-S3 (BTCAP free / largest_blk):
		 *
		 *   after network_prov_mgr_start_provisioning   44783 / 24576
		 *   before deferred subsystem start              36007 / 22528
		 *   after  deferred subsystem start              18007 / 11776
		 *   mqtt_io_start() then failed at                4027 /  2688
		 *
		 * 36 KB cannot hold MQTT's ~32 KB plus the codec's I2S buffers. Starting
		 * them here took the device down: audio_bsp_init() reached ESP_ERROR_CHECK
		 * with a failed i2s_new_channel() and aborted the chip on core 1.
		 *
		 * So restart deliberately instead. The credentials are already committed to
		 * NVS by the time WIFI_CONNECTED_EVENT fires, so the next boot takes the
		 * "Already provisioned" path where no BTDM is ever loaded and there is
		 * ~120 KB free with a 31 KB largest block -- enough for every subsystem.
		 */
		download::log_heap_info("provisioning complete, restarting");
		fflush(stdout);
		esp_restart();
	}

	/*
	 * Already-provisioned boot: the provisioning transport was never started, so
	 * there is no BTDM to wait for and the subsystems held back from app_main can
	 * come up straight away. See provisioning.hpp.
	 */
	if (s_post_provision_hook != nullptr)
	{
		download::log_heap_info("before deferred subsystem start");
		s_post_provision_hook();
		download::log_heap_info("after deferred subsystem start");
	}

	// Clean up binary image representation asset
	if (ui_lock(-1))
	{
		if (qr_image_obj != NULL)
		{
			ESP_LOGI(TAG, "Wi-Fi Up! Cleared binary image QR matrix widget.");
			lv_obj_delete(qr_image_obj);
			qr_image_obj = NULL;
		}
		if (qr_pixel_buffer != NULL)
		{
			heap_caps_free(qr_pixel_buffer);
			qr_pixel_buffer = NULL;
		}
		lv_obj_invalidate(lv_screen_active());
		ui_unlock();
	}

	/* All subsystems are up: start the download pipeline, then MQTT. */
	download::start();

	/*
	 * esp-mqtt needs ~6 KB of contiguous internal RAM for mqtt_task. On a
	 * first-time provisioning boot the Bluetooth controller (BTDM) still holds
	 * that memory here, so the first attempt can fail to create the task.
	 * Provisioning teardown is left to the client / the network_provisioning
	 * auto-stop timer (CONFIG_NETWORK_PROV_AUTOSTOP_TIMEOUT), which returns
	 * BTDM shortly afterwards - so just keep trying until there is room.
	 */
	bool mqtt_up = false;
	for (int attempt = 1; attempt <= MQTT_START_MAX_ATTEMPTS; attempt++)
	{
		if (mqtt_io_start() == ESP_OK)
		{
			download::log_heap_info("mqtt_io_start succeeded");
			mqtt_up = true;
			break;
		}

		ESP_LOGW(TAG, "MQTT start attempt %d/%d failed", attempt, MQTT_START_MAX_ATTEMPTS);
		download::log_heap_info("mqtt_io_start failed, retrying");
		vTaskDelay(pdMS_TO_TICKS(1000));
	}

	if (!mqtt_up)
	{
		ESP_LOGE(TAG, "MQTT client not started after %d attempts; running without cloud connectivity",
				 MQTT_START_MAX_ATTEMPTS);
	}

	while (1)
	{
		vTaskDelay(pdMS_TO_TICKS(1000));
	}
}
