Savio-Cardoz/theLink/components/sdcard_manager/i_filesystem.hpp

#pragma once
#include <cstdint>
#include <string>

/** 
 * @brief Abstract interface for file system operations
 */
class IFileSystem {
public:
    virtual ~IFileSystem() = default;

    // Hardware / Mount management
    virtual bool mount() = 0;
    virtual void unmount() = 0;
    virtual bool isMounted() const = 0;

    // Capacity of the mounted volume, for diagnostics. Both outputs are zeroed
    // and false is returned when there is no volume or it cannot be queried, so
    // callers never have to guess whether the numbers are meaningful.
    virtual bool getSpaceInfo(uint64_t &totalBytes, uint64_t &freeBytes) const = 0;

    // Core File Operations
    virtual bool fileExists(const std::string& path) const = 0;
    virtual bool deleteFile(const std::string& path) = 0;
    
    // Atomic rename is critical for our manifest safety (tmp -> json)
    virtual bool renameFile(const std::string& oldPath, const std::string& newPath) = 0;

    // High-level read/write for small files (like manifest.json)
    virtual bool readTextFile(const std::string& path, std::string& outContent) = 0;
    virtual bool writeTextFile(const std::string& path, const std::string& content) = 0;

    // Note: For large OTA binary flashing, we will use standard fopen/fread 
    // inside the Factory app to stream data, rather than loading 4MB into RAM.
};
